zapta/simple_stepper_motor_analyzer/kicad/stepper_analyzer.png

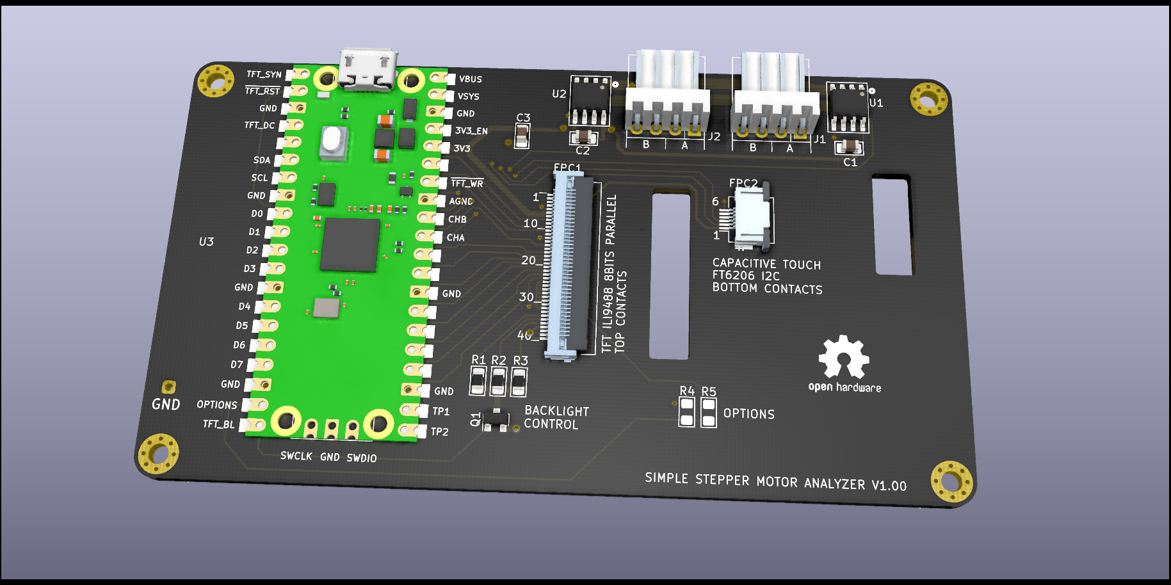
kicad/stepper_analyzer.png
