zapta/simple_stepper_motor_analyzer/platformio/src/display/mk3_lookup_tables.cpp

#include "mk3_lookup_tables.h"

// Tables were generated using the mk3_lookup_tables_generator.py script.

namespace mk3_lookup_tables {

const uint16_t color8_to_color16_table[] = {
    0x0000, 0x000a, 0x0015, 0x001f,  // 0x00 - 0x03
    0x0120, 0x012a, 0x0135, 0x013f,  // 0x04 - 0x07
    0x0240, 0x024a, 0x0255, 0x025f,  // 0x08 - 0x0b
    0x0360, 0x036a, 0x0375, 0x037f,  // 0x0c - 0x0f
    0x0480, 0x048a, 0x0495, 0x049f,  // 0x10 - 0x13
    0x05a0, 0x05aa, 0x05b5, 0x05bf,  // 0x14 - 0x17
    0x06c0, 0x06ca, 0x06d5, 0x06df,  // 0x18 - 0x1b
    0x07e0, 0x07ea, 0x07f5, 0x07ff,  // 0x1c - 0x1f
    0x2000, 0x200a, 0x2015, 0x201f,  // 0x20 - 0x23
    0x2120, 0x212a, 0x2135, 0x213f,  // 0x24 - 0x27
    0x2240, 0x224a, 0x2255, 0x225f,  // 0x28 - 0x2b
    0x2360, 0x236a, 0x2375, 0x237f,  // 0x2c - 0x2f
    0x2480, 0x248a, 0x2495, 0x249f,  // 0x30 - 0x33
    0x25a0, 0x25aa, 0x25b5, 0x25bf,  // 0x34 - 0x37
    0x26c0, 0x26ca, 0x26d5, 0x26df,  // 0x38 - 0x3b
    0x27e0, 0x27ea, 0x27f5, 0x27ff,  // 0x3c - 0x3f
    0x4800, 0x480a, 0x4815, 0x481f,  // 0x40 - 0x43
    0x4920, 0x492a, 0x4935, 0x493f,  // 0x44 - 0x47
    0x4a40, 0x4a4a, 0x4a55, 0x4a5f,  // 0x48 - 0x4b
    0x4b60, 0x4b6a, 0x4b75, 0x4b7f,  // 0x4c - 0x4f
    0x4c80, 0x4c8a, 0x4c95, 0x4c9f,  // 0x50 - 0x53
    0x4da0, 0x4daa, 0x4db5, 0x4dbf,  // 0x54 - 0x57
    0x4ec0, 0x4eca, 0x4ed5, 0x4edf,  // 0x58 - 0x5b
    0x4fe0, 0x4fea, 0x4ff5, 0x4fff,  // 0x5c - 0x5f
    0x6800, 0x680a, 0x6815, 0x681f,  // 0x60 - 0x63
    0x6920, 0x692a, 0x6935, 0x693f,  // 0x64 - 0x67
    0x6a40, 0x6a4a, 0x6a55, 0x6a5f,  // 0x68 - 0x6b
    0x6b60, 0x6b6a, 0x6b75, 0x6b7f,  // 0x6c - 0x6f
    0x6c80, 0x6c8a, 0x6c95, 0x6c9f,  // 0x70 - 0x73
    0x6da0, 0x6daa, 0x6db5, 0x6dbf,  // 0x74 - 0x77
    0x6ec0, 0x6eca, 0x6ed5, 0x6edf,  // 0x78 - 0x7b
    0x6fe0, 0x6fea, 0x6ff5, 0x6fff,  // 0x7c - 0x7f
    0x9000, 0x900a, 0x9015, 0x901f,  // 0x80 - 0x83
    0x9120, 0x912a, 0x9135, 0x913f,  // 0x84 - 0x87
    0x9240, 0x924a, 0x9255, 0x925f,  // 0x88 - 0x8b
    0x9360, 0x936a, 0x9375, 0x937f,  // 0x8c - 0x8f
    0x9480, 0x948a, 0x9495, 0x949f,  // 0x90 - 0x93
    0x95a0, 0x95aa, 0x95b5, 0x95bf,  // 0x94 - 0x97
    0x96c0, 0x96ca, 0x96d5, 0x96df,  // 0x98 - 0x9b
    0x97e0, 0x97ea, 0x97f5, 0x97ff,  // 0x9c - 0x9f
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
};

}  // namespace mk3_lookup_tables
