zapta/simple_stepper_motor_analyzer/platformio/src/display/lookup_tables_mk2.h

#pragma once

#include <stdint.h>

namespace lookup_tables_mk2 {

extern const uint32_t gpio_direct_set_table[];
extern const uint32_t gpio_direct_clr_table[];
extern const uint32_t gpio_color_set_table[];
extern const uint32_t gpio_color_clr_table[];

}  // namespace lookup_tables_mk2
