zapta/simple_stepper_motor_analyzer/platformio/src/ui/screen_manager.cpp

#include "screen_manager.h"

#include <stdio.h>

#include "acquisition/analyzer.h"
#include "current_histogram_screen.h"
#include "display/lvgl_adapter.h"
#include "home_screen.h"
#include "osciloscope_screen.h"
#include "phase_screen.h"
#include "pico/time.h"
#include "retraction_chart_screen.h"
#include "settings_screen.h"
#include "speed_gauge_screen.h"
#include "steps_chart_screen.h"
#include "steps_histogram_screen.h"
#include "test_screen.h"
#include "time_histogram_screen.h"

namespace screen_manager {

// A temp formatting buffer for the screens.
static char format_buffer[300];

const char* Screen::format(const char* format, ...) {
  va_list vl;
  va_start(vl, format);
  vsnprintf(format_buffer, sizeof(format_buffer), format, vl);
  va_end(vl);
  return format_buffer;
}

// Landing screen upon program start.
static constexpr ScreenId kInitialScreen = SCREEN_HOME;
// static constexpr ScreenId kInitialScreen = SCREEN_TEST;

struct ScreenDesc {
  ScreenId screen_id;
  Screen* screen_ptr;
};

static HomeScreen home_screen;
static SpeedGaugeScreen speed_gauge_screen;
static StepsChartScreen steps_chart_screen;
static RetractionChartScreen retraction_chart_screen;
static TimeHistogramScreen screen_time_histogram;
static StepsHistorgramScreen steps_histogram_screen;
static OsciloscopeScreen osciloscope_screen;
static PhaseScreen phase_screen;
static CurrentHistogramScreen current_histogram_screen;

// Order here determines screen 'next/previous' order.
static const ScreenDesc screen_table[] = {
    {SCREEN_HOME, &home_screen},
    {SCREEN_SPEED_GAUGE, &speed_gauge_screen},
    {SCREEN_STEPS_CHART, &steps_chart_screen},
    {SCREEN_RETRACTION_CHART, &retraction_chart_screen},
    {SCREEN_TIME_HISTOGRAM, &screen_time_histogram},
    {SCREEN_STEPS_HISTOGRAM, &steps_histogram_screen},
    {SCREEN_CURRENT_HISTOGRAM, &current_histogram_screen},
    {SCREEN_OSCILOSCOPE, &osciloscope_screen},
    {SCREEN_PHASE, &phase_screen},
};
constexpr int kNumScreens = sizeof(screen_table) / sizeof(screen_table[0]);

// Settings screen is not part of the screen sequence.
static SettingsScreen screen_settings;
static const ScreenDesc settings_screen_descriptor = {SCREEN_SETTINGS,
                                                      &screen_settings};

// Test screen is not part of the screen sequence.
static TestScreen screen_test;
static const ScreenDesc test_screen_descriptor = {SCREEN_TEST, &screen_test};

static const ScreenDesc* current_screen_desc = nullptr;

// If screen is not setup yet do it now.
static void maybe_setup_screen(const ScreenDesc* desc, uint8_t screen_num) {
  if (desc->screen_ptr->is_setup()) {
    return;
  }
  printf("Setting up screen %hhu\n", screen_num);
  desc->screen_ptr->setup(screen_num);
}

// Finds the screen descriptor in table. Returns null if not found.
static const ScreenDesc* find_screen_desc(ScreenId screen_id, int offset) {
  // TODO: Consider setting a secondary list of out of sequence screens in
  //  order to generalize the handling of those screens.
  //
  if (screen_id == SCREEN_SETTINGS) {
    // We ignore the offset since Setting screen is not in the
    // main screen sequence.
    maybe_setup_screen(&settings_screen_descriptor, 0);
    return &settings_screen_descriptor;
  }

  if (screen_id == SCREEN_TEST) {
    // We ignore the offset since Test screen is not in the
    // main screen sequence.
    maybe_setup_screen(&test_screen_descriptor, 0);
    return &test_screen_descriptor;
  }

  // Try to match to the sequential screens.
  for (int i = 0; i < kNumScreens; i++) {
    if (screen_id == screen_table[i].screen_id) {
      int idx = (i + offset) % kNumScreens;
      if (idx < 0) {
        idx += kNumScreens;
      }
      // Here idx is in [0, kNumScreens).
      const ScreenDesc* new_screen_desc = &screen_table[idx];
      maybe_setup_screen(new_screen_desc, idx + 1);
      return new_screen_desc;
    }
  }
  return nullptr;
}

static void switch_screen(ScreenId screen_id, int offset) {
  ui_events::clear_pending_events();
  const ScreenId current_screen_id = current_screen_desc->screen_id;
  const ScreenDesc* new_screen_desc = find_screen_desc(screen_id, offset);
  if (new_screen_desc == nullptr ||
      new_screen_desc->screen_id == current_screen_id) {
    return;
  }
  current_screen_desc->screen_ptr->on_unload();
  new_screen_desc->screen_ptr->on_load();
  current_screen_desc = new_screen_desc;
  lv_scr_load(current_screen_desc->screen_ptr->lv_scr());
}

// Common to all screens.
// Returns true if event should also be propagated to the screen.
static bool common_event_handler(ui_events::UiEventId ui_event_id) {
  // Handle at this level
  switch (ui_event_id) {
    case ui_events::UI_EVENT_RESET:
      analyzer::reset_state();
      return true;

    case ui_events::UI_EVENT_PREV_PAGE:
      switch_screen(current_screen_desc->screen_id, -1);
      return false;

    case ui_events::UI_EVENT_HOME_PAGE:
      switch_screen(SCREEN_HOME, 0);
      return false;

    case ui_events::UI_EVENT_NEXT_PAGE:
      switch_screen(current_screen_desc->screen_id, 1);
      return false;

    case ui_events::UI_EVENT_SCREENSHOT:
      // We assume that LVGL doesn't call an event during
      // a screen update so it should be safe to access the TFT to read
      // the data. Otherwise, we could buffer the request and dump
      // in loop(), outside of LVGL.
      lvgl_adapter::dump_screen();
      return false;

    case ui_events::UI_EVENT_SETTINGS:
      switch_screen(SCREEN_SETTINGS, 0);
      return false;

    default:
      return true;
  }
}

void setup() {
  // We start with on demand setup() of first screen.
  // Soon after this function return we setup the
  // rest of the screen. This shaves about 1sec from
  // the startup time up to first screen.

  // Select initial screen.
  current_screen_desc = find_screen_desc(kInitialScreen, 0);
  current_screen_desc->screen_ptr->on_load();
  lv_scr_load(current_screen_desc->screen_ptr->lv_scr());
}

void setup_screens_ahead() {
  for (int i = 0; i < kNumScreens; i++) {
    maybe_setup_screen(&screen_table[i], i + 1);
  }
  maybe_setup_screen(&settings_screen_descriptor, 0);
}

void loop() {
  // Handle pending ui event, if any.
  ui_events::UiEventId event_id;
  if (ui_events::consume_event(&event_id)) {
    const bool also_send_to_screen = common_event_handler(event_id);
    if (also_send_to_screen) {
      current_screen_desc->screen_ptr->on_event(event_id);
    }
  }

  // Service the current screen.
  current_screen_desc->screen_ptr->loop();
};

}  // namespace screen_manager
